sdoira/U96-SVM/src/design_1/hdl/design_1_wrapper.v

//Copyright 1986-2020 Xilinx, Inc. All Rights Reserved.
//--------------------------------------------------------------------------------
//Tool Version: Vivado v.2020.1_AR75325 (win64) Build 2902540 Wed May 27 19:54:49 MDT 2020
//Date        : Wed Dec  2 00:59:34 2020
//Host        : m-Book running 64-bit major release  (build 9200)
//Command     : generate_target design_1_wrapper.bd
//Design      : design_1_wrapper
//Purpose     : IP block netlist
//--------------------------------------------------------------------------------
`timescale 1 ps / 1 ps

module design_1_wrapper
   (clk_out1_0,
    gpio_in_0,
    led_0,
    mipi_phy_if_0_clk_n,
    mipi_phy_if_0_clk_p,
    mipi_phy_if_0_data_n,
    mipi_phy_if_0_data_p,
    mipi_phy_if_1_clk_n,
    mipi_phy_if_1_clk_p,
    mipi_phy_if_1_data_n,
    mipi_phy_if_1_data_p);
  output clk_out1_0;
  input [1:0]gpio_in_0;
  output [1:0]led_0;
  input mipi_phy_if_0_clk_n;
  input mipi_phy_if_0_clk_p;
  input [1:0]mipi_phy_if_0_data_n;
  input [1:0]mipi_phy_if_0_data_p;
  input mipi_phy_if_1_clk_n;
  input mipi_phy_if_1_clk_p;
  input [1:0]mipi_phy_if_1_data_n;
  input [1:0]mipi_phy_if_1_data_p;

  wire clk_out1_0;
  wire [1:0]gpio_in_0;
  wire [1:0]led_0;
  wire mipi_phy_if_0_clk_n;
  wire mipi_phy_if_0_clk_p;
  wire [1:0]mipi_phy_if_0_data_n;
  wire [1:0]mipi_phy_if_0_data_p;
  wire mipi_phy_if_1_clk_n;
  wire mipi_phy_if_1_clk_p;
  wire [1:0]mipi_phy_if_1_data_n;
  wire [1:0]mipi_phy_if_1_data_p;

  design_1 design_1_i
       (.clk_out1_0(clk_out1_0),
        .gpio_in_0(gpio_in_0),
        .led_0(led_0),
        .mipi_phy_if_0_clk_n(mipi_phy_if_0_clk_n),
        .mipi_phy_if_0_clk_p(mipi_phy_if_0_clk_p),
        .mipi_phy_if_0_data_n(mipi_phy_if_0_data_n),
        .mipi_phy_if_0_data_p(mipi_phy_if_0_data_p),
        .mipi_phy_if_1_clk_n(mipi_phy_if_1_clk_n),
        .mipi_phy_if_1_clk_p(mipi_phy_if_1_clk_p),
        .mipi_phy_if_1_data_n(mipi_phy_if_1_data_n),
        .mipi_phy_if_1_data_p(mipi_phy_if_1_data_p));
endmodule
